SCiunczyk/wallbox-diy/HA/configuration.yaml

#
# CREATE some helpers for DomBusEVSE
input_number:
  ev3pselect: # Values 0/254
    name: EV3PSelect
    initial: 254
    min: 0
    max: 254
    step: 254
  evmaxcurrent: # Range: 6-36A
    name: EVMaxCurrent
    initial: 16
    min: 6
    max: 36
    step: 1
  evmaxgridpower: # Range: 1000-25000W
    name: EVMaxGridPower
    initial: 3300
    min: 3000
    max: 11000
    step: 100

  evstartpower: # Range: 800-25000W
    name: EVStartPower
    initial: 1600
    min: 800
    max: 4000
    step: 100
  evstoptime: # Range: 5-600s
    name: EVStopTime
    initial: 90
    min: 5
    max: 900
    step: 5
  evautostart: # Range: 0-1
    name: EVAutoStart
    initial: 1
    min: 0
    max: 1
    step: 1
  evmaxpower2: # Range: 0-25000W
    name: EVMaxPower2
    initial: 0
    min: 0
    max: 8000
    step: 100
  evmaxpowertime: # Range: 0-43200s
    name: EVMaxPowerTime
    initial: 0
    min: 0
    max: 43200
    step: 60
  evmaxpowertime2: # Range: 0-43200s
    name: EVMaxPowerTime2
    initial: 0
    min: 0
    max: 43200
    step: 60
  evwaittime: # Range: 3-60s
    name: EVWaitTime
    initial: 7
    min: 3
    max: 60
    step: 1
  evmetertype: # Range: 0-1
    name: EVMeterType
    initial: 1
    min: 0
    max: 1
    step: 1
input_select:
  evstatename:
    name: EVStateName
    options:
    - "Off"
    - Disconnected
    - Connected
    - Charging
    - Charging+Vent
    - Alarm EV
    - Alarm Power Outage
    - Alarm Welded
    initial: Disconnected
  evmodename:
    name: EVModeName
    options:
    - "Off"
    - Solar
    - 25%
    - 50%
    - 75%
    - 100%
    - Managed
    initial: "Off"
input_button:
  evmodeset:
    name: EVModeSet
input_boolean:
  ev3phasecharge:
    name: EV3PhaseCharge
    initial: True
